smdjeff/arcade-rom-2532/software/getchar_nonblock.c

#include <stdlib.h>
#include <stdint.h>
#include <stdbool.h>
#include <stdio.h>
#include <string.h>
#include <assert.h>
#include <unistd.h>
#include <fcntl.h>
#include <unistd.h>
#include <termios.h>

#include "getchar_nonblock.h"

    
int getchar_nonblock(void) {
    struct timeval tv;
    fd_set fds;
    tv.tv_sec = 0;
    tv.tv_usec = 0;
    FD_ZERO(&fds);
    FD_SET(STDIN_FILENO, &fds); //STDIN_FILENO is 0
    select(STDIN_FILENO+1, &fds, NULL, NULL, &tv);
    if ( FD_ISSET(STDIN_FILENO, &fds) != 0 ) {
       return fgetc( stdin );
    }
    return 0;
}

void nonblocking(bool enable) {
    struct termios ttystate = {0,};
    tcgetattr(STDIN_FILENO, &ttystate);
    if (enable) {
        ttystate.c_lflag &= ~ICANON;
        ttystate.c_cc[VMIN] = 1;
    } else {
        ttystate.c_lflag |= ICANON;
    }
    tcsetattr(STDIN_FILENO, TCSANOW, &ttystate);
}
